f1rmb/MMDVM_HS_Hat-Enclosure/Parts/OLED_27x27.STEP

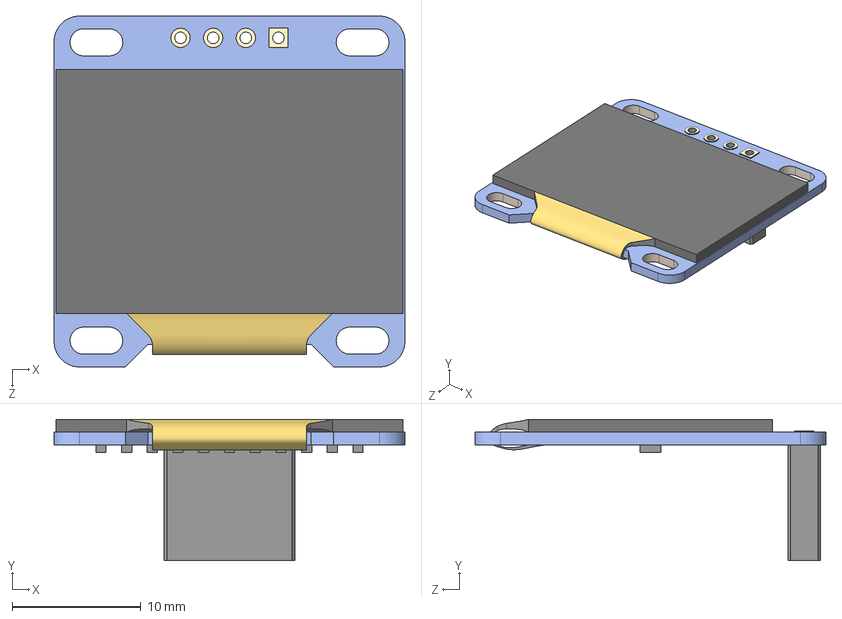
[picture p17: CAD file, 2018-05-28]
Parts/OLED_27x27.STEP
27.3 x 11.0 x 27.3 mm
