f1rmb/MMDVM_HS_Hat-Enclosure/Parts/PinHeader_1x04_P2.54mm_Vertical.step

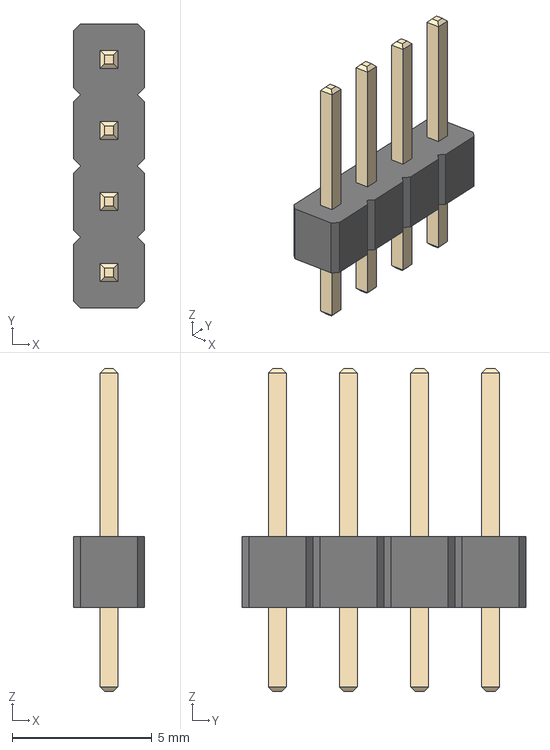
[picture p18: CAD file, 2018-05-28]
Parts/PinHeader_1x04_P2.54mm_Vertical.step
2.54 x 10.2 x 11.5 mm
