f1rmb/MMDVM_HS_Hat-Enclosure/Parts/PinHeader_2x20_P2.54mm_Vertical.step

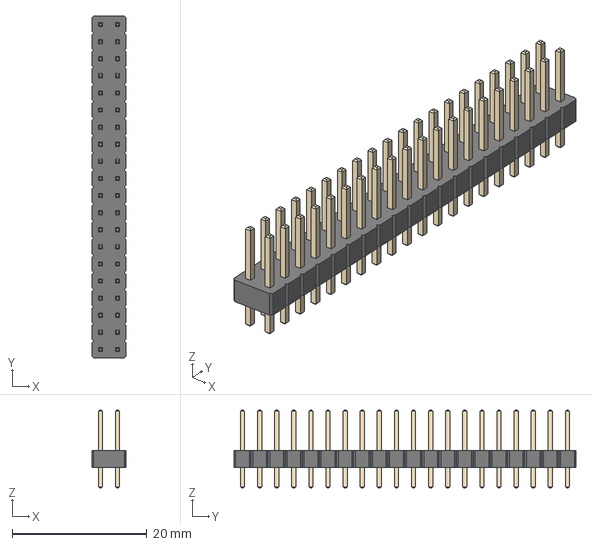
[picture p19: CAD file, 2018-05-28]
Parts/PinHeader_2x20_P2.54mm_Vertical.step
5.08 x 50.8 x 11.5 mm
