f1rmb/MMDVM_HS_Hat-Enclosure/Parts/Micro SD Card.STEP

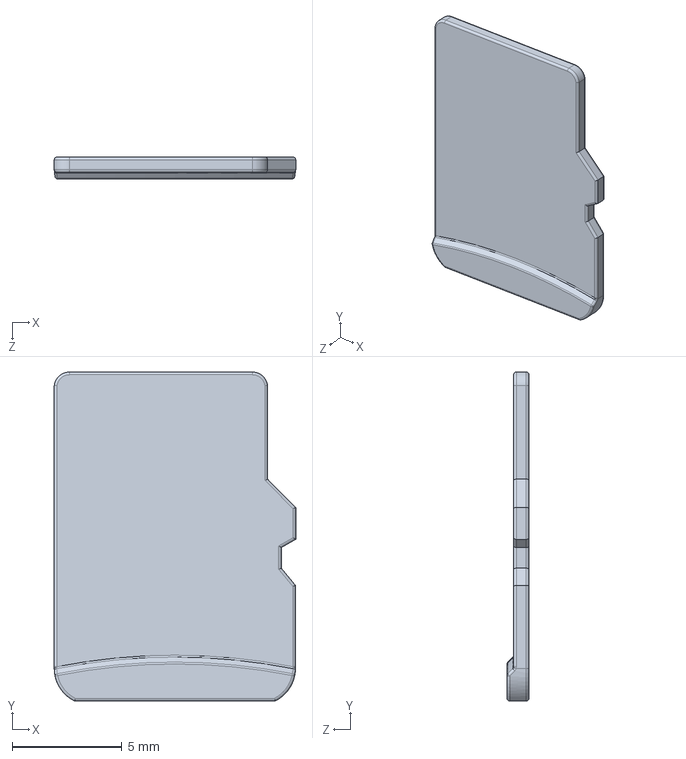
[picture p20: CAD file, 2018-05-26]
Parts/Micro SD Card.STEP
11.0 x 15.0 x 1.00 mm
